yet-another-average-joe/MarlinOctoHat/_pictures/DSC_8483.JPG

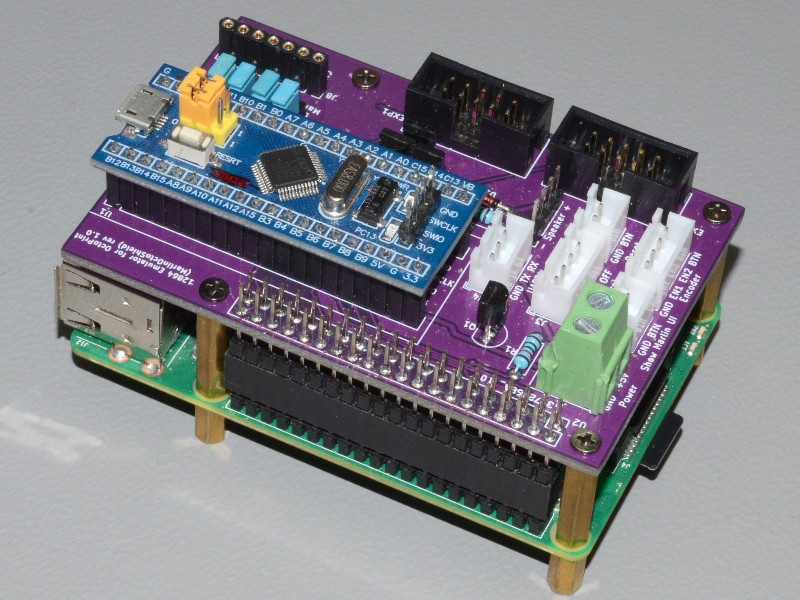
_pictures/DSC_8483.JPG
